mariusmym/WLED-MiniDuo-SR-PJ/Images/IMG_7985.JPEG

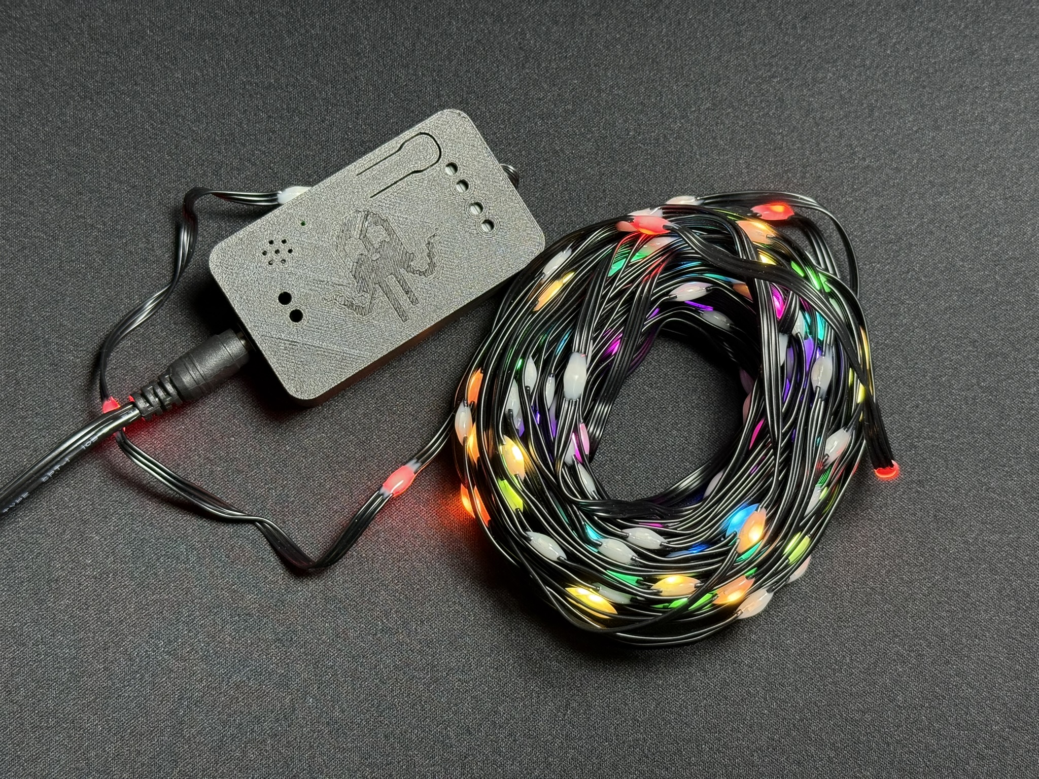
Images/IMG_7985.JPEG
